jstanley0/music-box/firmware/songs.c

#include <avr/pgmspace.h>
#include "songs.h"

// song format

// note (N == midi_note - 35)
//  7  6  5  4  3  2  1  0
//  0  0 N5 N4 N3 N2 N1 N0

// delay (D == delay_in_ms / 10)
//  7  6  5  4  3  2  1  0
//  0  1 D5 D4 D3 D2 D1 D0

// noise (N == noise type, A = attenuated; S = sustain cycles - 1)
//  7  6  5  4  3  2  1  0
//  1  0 A0 S1 S0 N2 N1 N0

// end song
//  7  6  5  4  3  2  1  0
//  1  1  1  1  1  1  1  1

const uint16_t note_table[64] PROGMEM = {1012,956,902,851,804,758,716,676,638,602,568,536,506,478,451,426,402,379,358,338,319,301,284,268,253,239,225,213,201,190,179,169,159,150,142,134,127,119,113,106,100,95,89,84,80,75,71,67,63,60,56,53,50,47,45,42,40,38,36,34,32,30,28,27,};
const uint8_t st_elsewhere[] PROGMEM = {0x1e,0x5c,0x17,0x5c,0x19,0x5c,0x1e,0x5c,0x20,0x5c,0x19,0x5d,0x1e,0x5c,0x20,0x5c,0x25,0x5c,0x1e,0x5c,0x20,0x5c,0x25,0x5d,0x29,0x5c,0x20,0x5c,0x25,0x5c,0x29,0x5c,0x6,0x25,0x2a,0x86,0x5c,0x6,0xb4,0x5d,0x6,0x84,0x5c,0x6,0x86,0x5c,0x6,0x86,0x5c,0x6,0x31,0x86,0x5c,0x6,0x36,0x84,0x5c,0x6,0x38,0x3d,0xb4,0x5d,0x6,0x86,0x5c,0x6,0xb4,0x5c,0x6,0x84,0x5c,0x6,0x86,0x5c,0x6,0x19,0x1e,0x86,0x5c,0x6,0x19,0x20,0x86,0x5d,0x6,0x1e,0x22,0x84,0x5c,0x6,0x1e,0x23,0xb4,0x5c,0x6,0x86,0x5c,0x6,0x23,0xb4,0x5c,0x6,0x1e,0x22,0x84,0x5c,0x6,0x86,0x5d,0x6,0x19,0x20,0x86,0x5c,0x6,0x20,0x25,0x86,0x5c,0x6,0x20,0x25,0x84,0x5c,0x6,0x20,0x25,0xb4,0x5c,0x6,0x86,0x5c,0x6,0x25,0xb4,0x5d,0x6,0x1e,0x22,0x84,0x5c,0x6,0x86,0x5c,0x6,0x19,0x1e,0x86,0x5c,0x6,0x19,0x20,0x86,0x5c,0x6,0x1e,0x22,0x84,0x5c,0x6,0x1e,0x23,0xb4,0x5d,0x6,0x86,0x5c,0x6,0x23,0xb4,0x5c,0x6,0x1e,0x22,0x84,0x5c,0x6,0x19,0x1e,0x86,0x5c,0x6,0x1d,0x20,0x86,0x5d,0x6,0x86,0x5c,0x6,0x1d,0x20,0x84,0x5c,0x6,0xb4,0x5c,0x6,0x1e,0x22,0x86,0x5c,0x6,0xb4,0x5c,0x6,0x84,0x5d,0x6,0x86,0x5c,0x6,0x19,0x1e,0x86,0x5c,0x6,0x19,0x20,0x86,0x5c,0x6,0x1e,0x22,0x84,0x5c,0x6,0x1e,0x23,0xb4,0x5c,0x6,0x86,0x5d,0x6,0x23,0xb4,0x5c,0x6,0x1e,0x22,0x84,0x5c,0x6,0x86,0x5c,0x6,0x19,0x20,0x86,0x5c,0x6,0x20,0x25,0x86,0x5c,0x6,0x20,0x25,0x84,0x5d,0x6,0x20,0x25,0xb4,0x5c,0x6,0x86,0x5c,0x6,0x25,0xb4,0x5c,0x6,0x1e,0x22,0x84,0x5c,0x6,0x86,0x5c,0x6,0x19,0x1e,0x86,0x5d,0x6,0x19,0x20,0x86,0x5c,0x6,0x1e,0x22,0x84,0x5c,0x6,0x1e,0x23,0xb4,0x5c,0x6,0x86,0x5c,0x6,0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
x2f,0x36,0xb4,0x5d,0x1,0x86,0x7f,0x55,0x1,0x84,0x5c,0x1,0x22,0x86,0x5c,0x20,0x86,0x5d,0x1e,0x84,0x5c,0x14,0x1e,0xb4,0x5c,0x14,0x86,0x5c,0x12,0xb4,0x5c,0x17,0x84,0x5c,0x14,0x19,0x86,0x5d,0x14,0x1e,0x86,0x5c,0x25,0x86,0x5c,0x2a,0x84,0x5c,0x6,0x16,0x31,0xb4,0x5c,0x6,0x16,0x84,0x7f,0x7f,0x7f,0x65,0xff};
const uint8_t macgyver[] PROGMEM = {0x5,0x18,0x29,0x86,0x59,0x1d,0x59,0x22,0x5a,0x24,0x86,0x59,0x22,0x5a,0x18,0x59,0x1d,0x5a,0x18,0x72,0x1d,0x86,0x5a,0x22,0x59,0x24,0x86,0x5a,0x22,0x59,0x1d,0x5a,0x3,0x18,0x27,0x59,0x1d,0x59,0x1,0xd,0x25,0x86,0x5a,0x1d,0x59,0x22,0x5a,0x24,0x86,0x59,0x22,0x5a,0x18,0x59,0x1d,0x59,0x18,0x73,0x22,0x86,0x5a,0x27,0x59,0x25,0x86,0x5a,0x3,0xf,0x27,0x59,0x25,0x59,0x24,0x5a,0x22,0x59,0x5,0x18,0x29,0x86,0x5a,0x1d,0x59,0x22,0x5a,0x24,0x86,0x59,0x22,0x59,0x18,0x5a,0x1d,0x59,0x18,0x73,0x1d,0x86,0x5a,0x22,0x59,0x24,0x86,0x59,0x22,0x5a,0x1d,0x59,0x3,0x18,0x27,0x5a,0x1d,0x59,0x1,0xd,0x25,0x86,0x5a,0x1d,0x59,0x22,0x59,0x24,0x86,0x5a,0x22,0x59,0x18,0x5a,0x1d,0x59,0x18,0x73,0x22,0x86,0x5a,0x27,0x59,0x25,0x86,0x59,0x3,0xf,0x27,0x5a,0x25,0x59,0x24,0x5a,0x22,0x59,0x8,0x20,0x24,0x86,0x5a,0x8,0x14,0x59,0x8,0x14,0x59,0x8,0x1f,0x24,0x86,0x5a,0x8,0x14,0x59,0x8,0x14,0x5a,0x8,0x14,0x59,0x8,0x14,0x5a,0x8,0x1d,0x24,0x86,0x59,0x8,0x14,0x59,0x8,0x14,0x5a,0x8,0x1c,0x22,0x86,0x59,0x8,0x14,0x5a,0x8,0x24,0x27,0x59,0x8,0x14,0x5a,0x8,0x14,0x59,0x8,0x20,0x24,0x86,0x59,0x8,0x14,0x5a,0x8,0x14,0x59,0x8,0x1f,0x24,0x86,0x5a,0x8,0x14,0x59,0x8,0x14,0x5a,0x8,0x14,0x59,0x8,0x14,0x59,0x1,0x20,0x24,0x86,0x73,0x3,0x1f,0x22,0x7f,0x7f,0x5b,0x3,0x22,0x25,0x86,0x59,0x3,0x22,0x25,0x86,0x5a,0x3,0x22,0x25,0x86,0x59,0x3,0x22,0x25,0x86,0x5a,0x3,0x22,0x25,0x86,0x59,0x3,0x22,0x25,0x86,0x59,0x3,0x22,0x25,0x86,0x5a,0x3,0x22,0x25,0x86,0x59,0x8,0x20,0x24,0xbc,0x5a,0x14,0x20,0x86,0x59,0x8,0x14,0x84,0x5a,0x14,0x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
x36,0x84,0x5e,0x6,0x22,0x84,0x5f,0x1b,0x27,0x33,0x84,0x5e,0x3,0x24,0x30,0x84,0x5f,0x8,0x1e,0x20,0x84,0x5e,0xa,0x22,0x2c,0x84,0x5f,0x0,0x1e,0x24,0x84,0x5e,0x1,0x25,0x29,0x84,0x5f,0x14,0x20,0x2c,0x84,0x5e,0x8,0x20,0x84,0x5f,0x14,0x25,0x31,0x84,0x5e,0x1,0x29,0x35,0x84,0x5f,0x8,0x1d,0x25,0x84,0x5e,0x0,0x27,0x33,0x84,0x5f,0x8,0x1b,0x1e,0x84,0x5e,0x1,0x25,0x31,0x84,0xff};
const uint8_t charlie_brown[] PROGMEM = {0x0,0x84,0x55,0x7,0x86,0x55,0xc,0x55,0x0,0x84,0x55,0x7,0x86,0x55,0xc,0x86,0x69,0x0,0x80,0x6a,0x7,0x84,0x55,0x9,0x55,0x0,0x84,0x55,0x7,0x86,0x55,0x9,0xbc,0x6a,0x0,0x86,0x6a,0x7,0x84,0x55,0xc,0x55,0x0,0x84,0x54,0x7,0x86,0x55,0xc,0x86,0x6a,0x0,0x80,0x6a,0x7,0x84,0x55,0x9,0x55,0x0,0x84,0x55,0x7,0x86,0x55,0x9,0xbc,0x6a,0x0,0x1c,0x24,0x84,0x69,0x7,0x1f,0x26,0x84,0x55,0xc,0x24,0x28,0x55,0x0,0x84,0x55,0x7,0x24,0x28,0x86,0x55,0xc,0x1f,0x26,0x86,0x55,0x1c,0x24,0x80,0x55,0x0,0x80,0x55,0x1f,0x26,0x84,0x55,0x7,0x86,0x55,0x9,0x55,0x0,0x1c,0x24,0x84,0x55,0x7,0x86,0x55,0x9,0xbc,0x69,0x0,0x1c,0x24,0x86,0x6a,0x7,0x1f,0x26,0x84,0x55,0xc,0x24,0x28,0x55,0x0,0x84,0x55,0x7,0x24,0x28,0x86,0x55,0xc,0x86,0x6a,0x0,0x80,0x6a,0x7,0x84,0x55,0x9,0x55,0x0,0x84,0x54,0x7,0x86,0x55,0x9,0xbc,0x6a,0x0,0x1c,0x24,0x84,0x6a,0x7,0x1f,0x26,0x84,0x55,0xc,0x24,0x28,0x55,0x0,0x84,0x55,0x7,0x24,0x28,0x86,0x55,0xc,0x1f,0x26,0x86,0x55,0x1c,0x24,0x80,0x55,0x0,0x80,0x55,0x1f,0x26,0x84,0x55,0x7,0x86,0x54,0x9,0x55,0x0,0x1c,0x24,0x84,0x55,0x7,0x86,0x55,0x9,0xbc,0x6a,0x3,0x1f,0x24,0x86,0x6a,0xa,0x84,0x55,0xf,0x55,0x3,0x1f,0x26,0x84,0x55,0xa,0x1f,0x26,0x86,0x55,0xf,0x86,0x6a,0x3,0x80,0x69,0xa,0x84,0x55,0xc,0x55,0x3,0x84,0x55,0xa,0x86,0x55,0xc,0xbc,0x6a,0x0,0x1c,0x24,0x86,0x6a,0x7,0x84,0x55,0xc,0x55,0x0,0x1f,0x26,0x84,0x55,0x7,0x1f,0x26,0x86,0x54,0xc,0x86,0x6a,0x0,0x80,0x6a,0x7,0x84,0x55,0x9,0x55,0x0,0x84,0x55,0x7,0x86,0x55,0x9,0xbc,0x6a,0x0,0x1c,0x24,0x84,0x6a,0x7,0x1f,0x26,0x84,0x55,0xc,0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
