jstanley0/music-box/firmware/songs.h

#pragma once

extern const uint16_t note_table[64] PROGMEM;

extern const uint8_t st_elsewhere[] PROGMEM;
extern const uint8_t macgyver[] PROGMEM;
extern const uint8_t quantum_leap[] PROGMEM;
extern const uint8_t hogans_heroes[] PROGMEM;
extern const uint8_t charlie_brown[] PROGMEM;
extern const uint8_t brooklet[] PROGMEM;
extern const uint8_t darker[] PROGMEM;
extern const uint8_t lament[] PROGMEM;
extern const uint8_t nervous[] PROGMEM;
